boomsya/PET-filament-maker/22.jpg

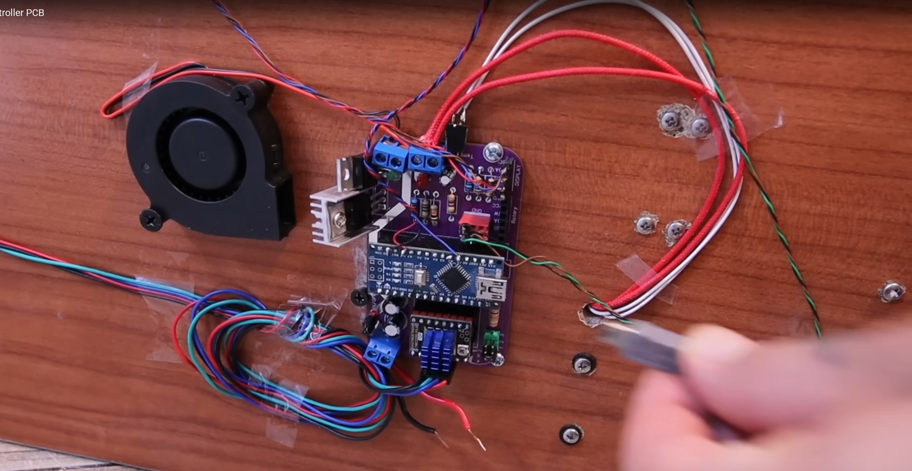
22.jpg
