boomsya/PET-filament-maker/24.jpg

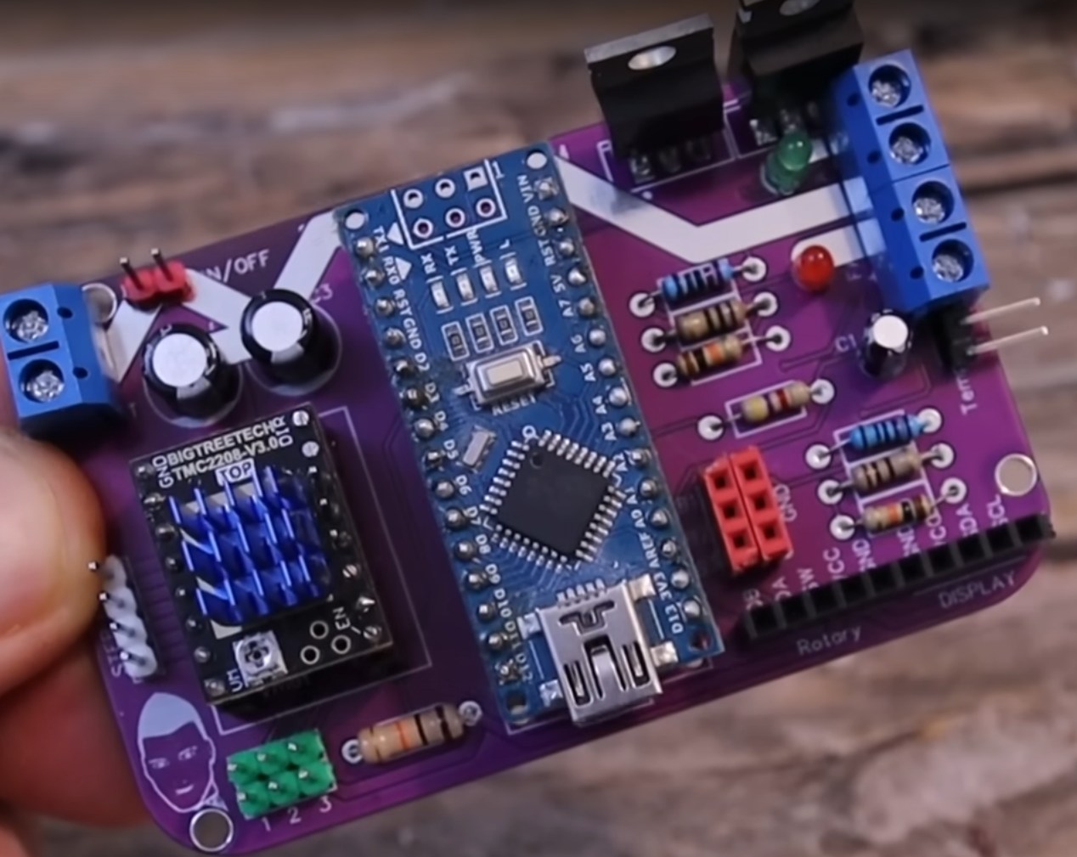
24.jpg
