boomsya/PET-filament-maker/20230709_185415.jpg

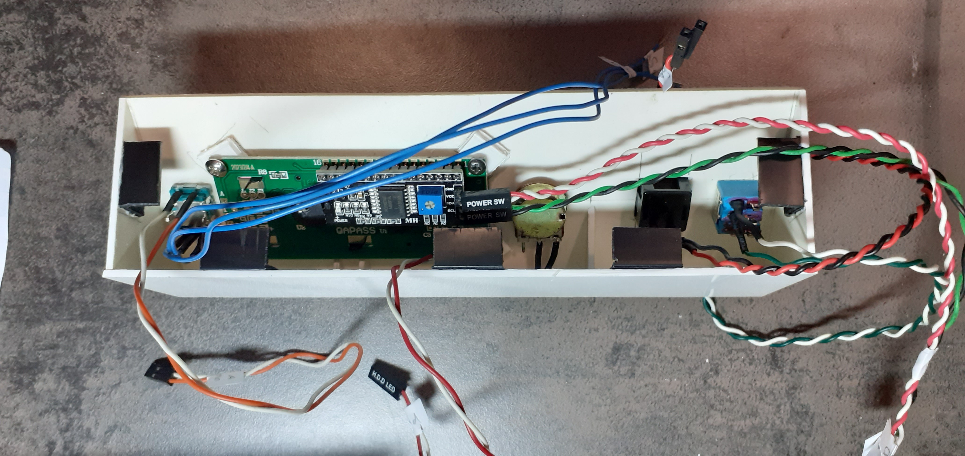
20230709_185415.jpg
