boomsya/PET-filament-maker/20230722_191305.jpg

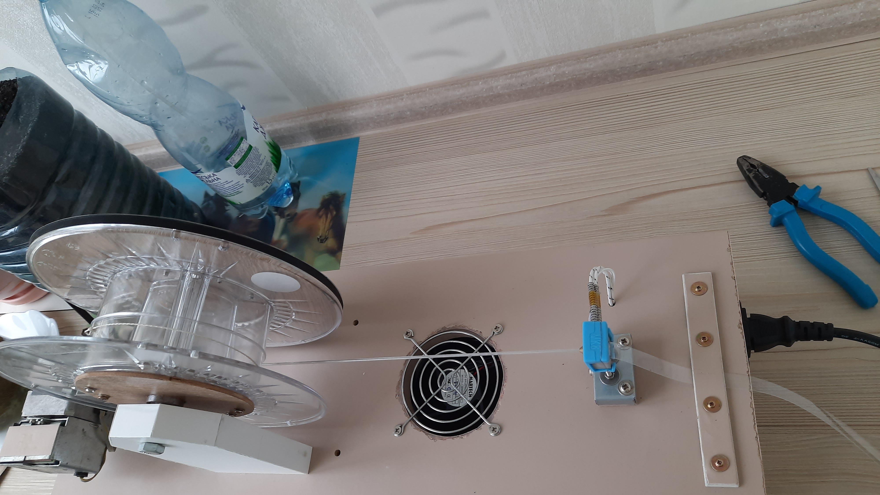
20230722_191305.jpg
