boomsya/PET-filament-maker/20230722_191311.jpg

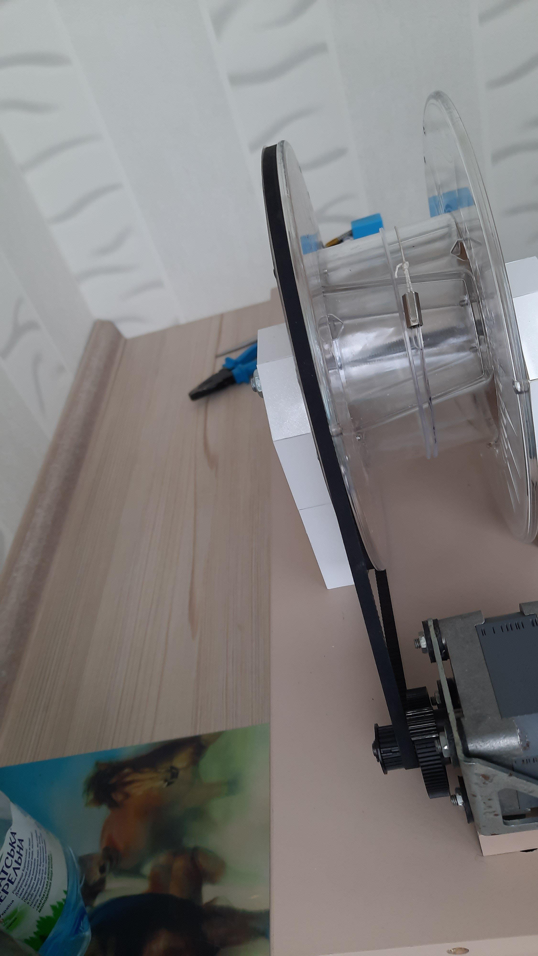
20230722_191311.jpg
