boomsya/PET-filament-maker/20230724_134259.jpg

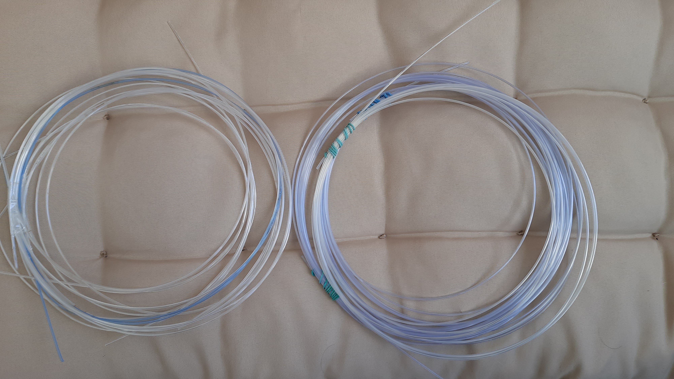
20230724_134259.jpg
