boomsya/PET-filament-maker/20230801_170722.jpg

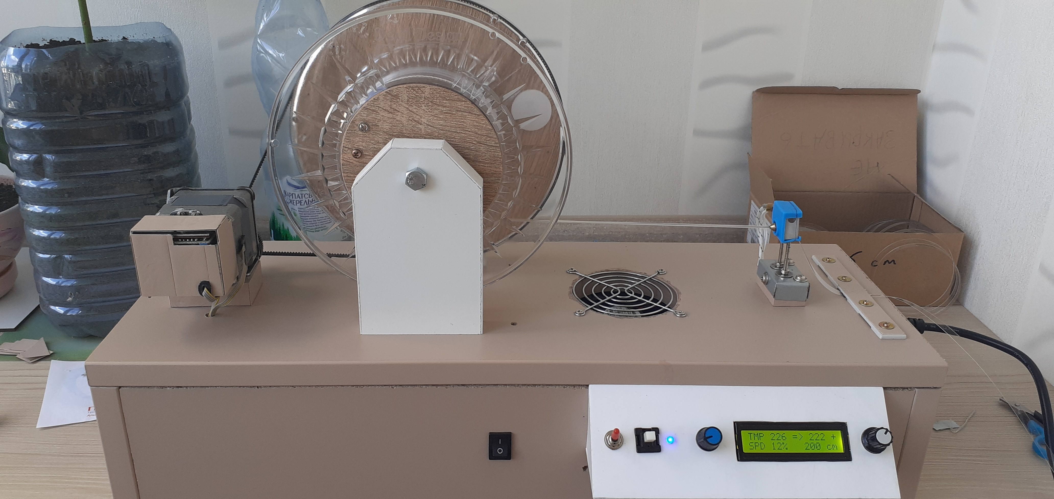
20230801_170722.jpg
