boomsya/PET-filament-maker/20230801_170733.jpg

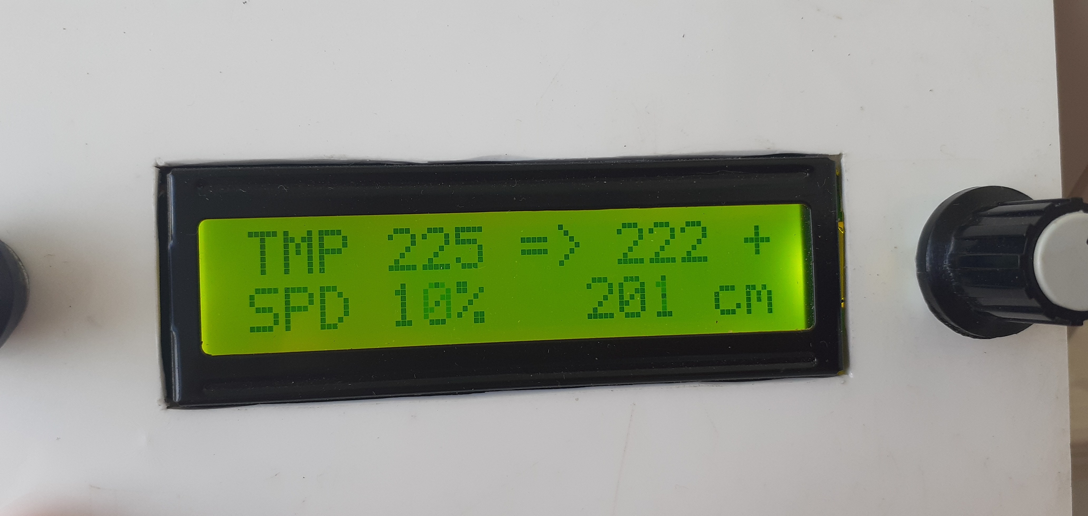
20230801_170733.jpg
