boomsya/PET-filament-maker/20231226_192626.jpg

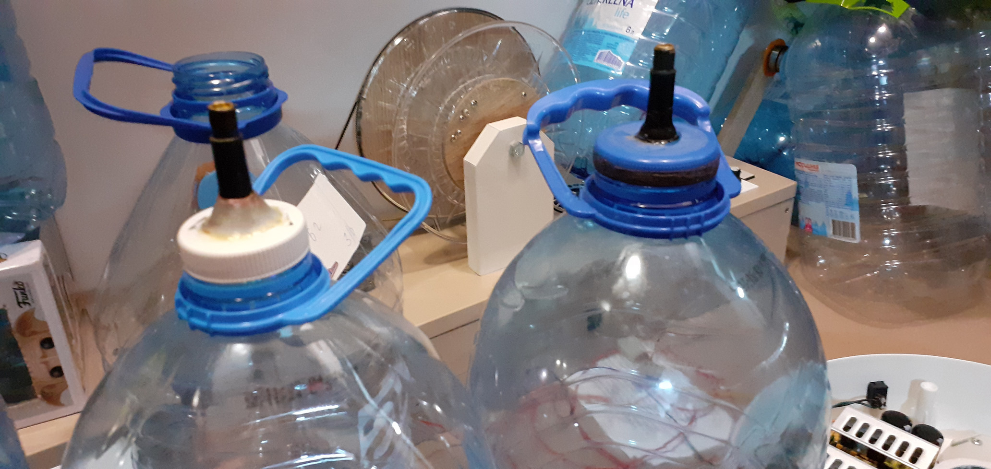
20231226_192626.jpg
